shinkaimayano/ttocyobitnA/KiCad Files/ttocyobItnA.kicad_sch

## KiCad design KiCad Files/ttocyobItnA.kicad_sch (2022-06-01)

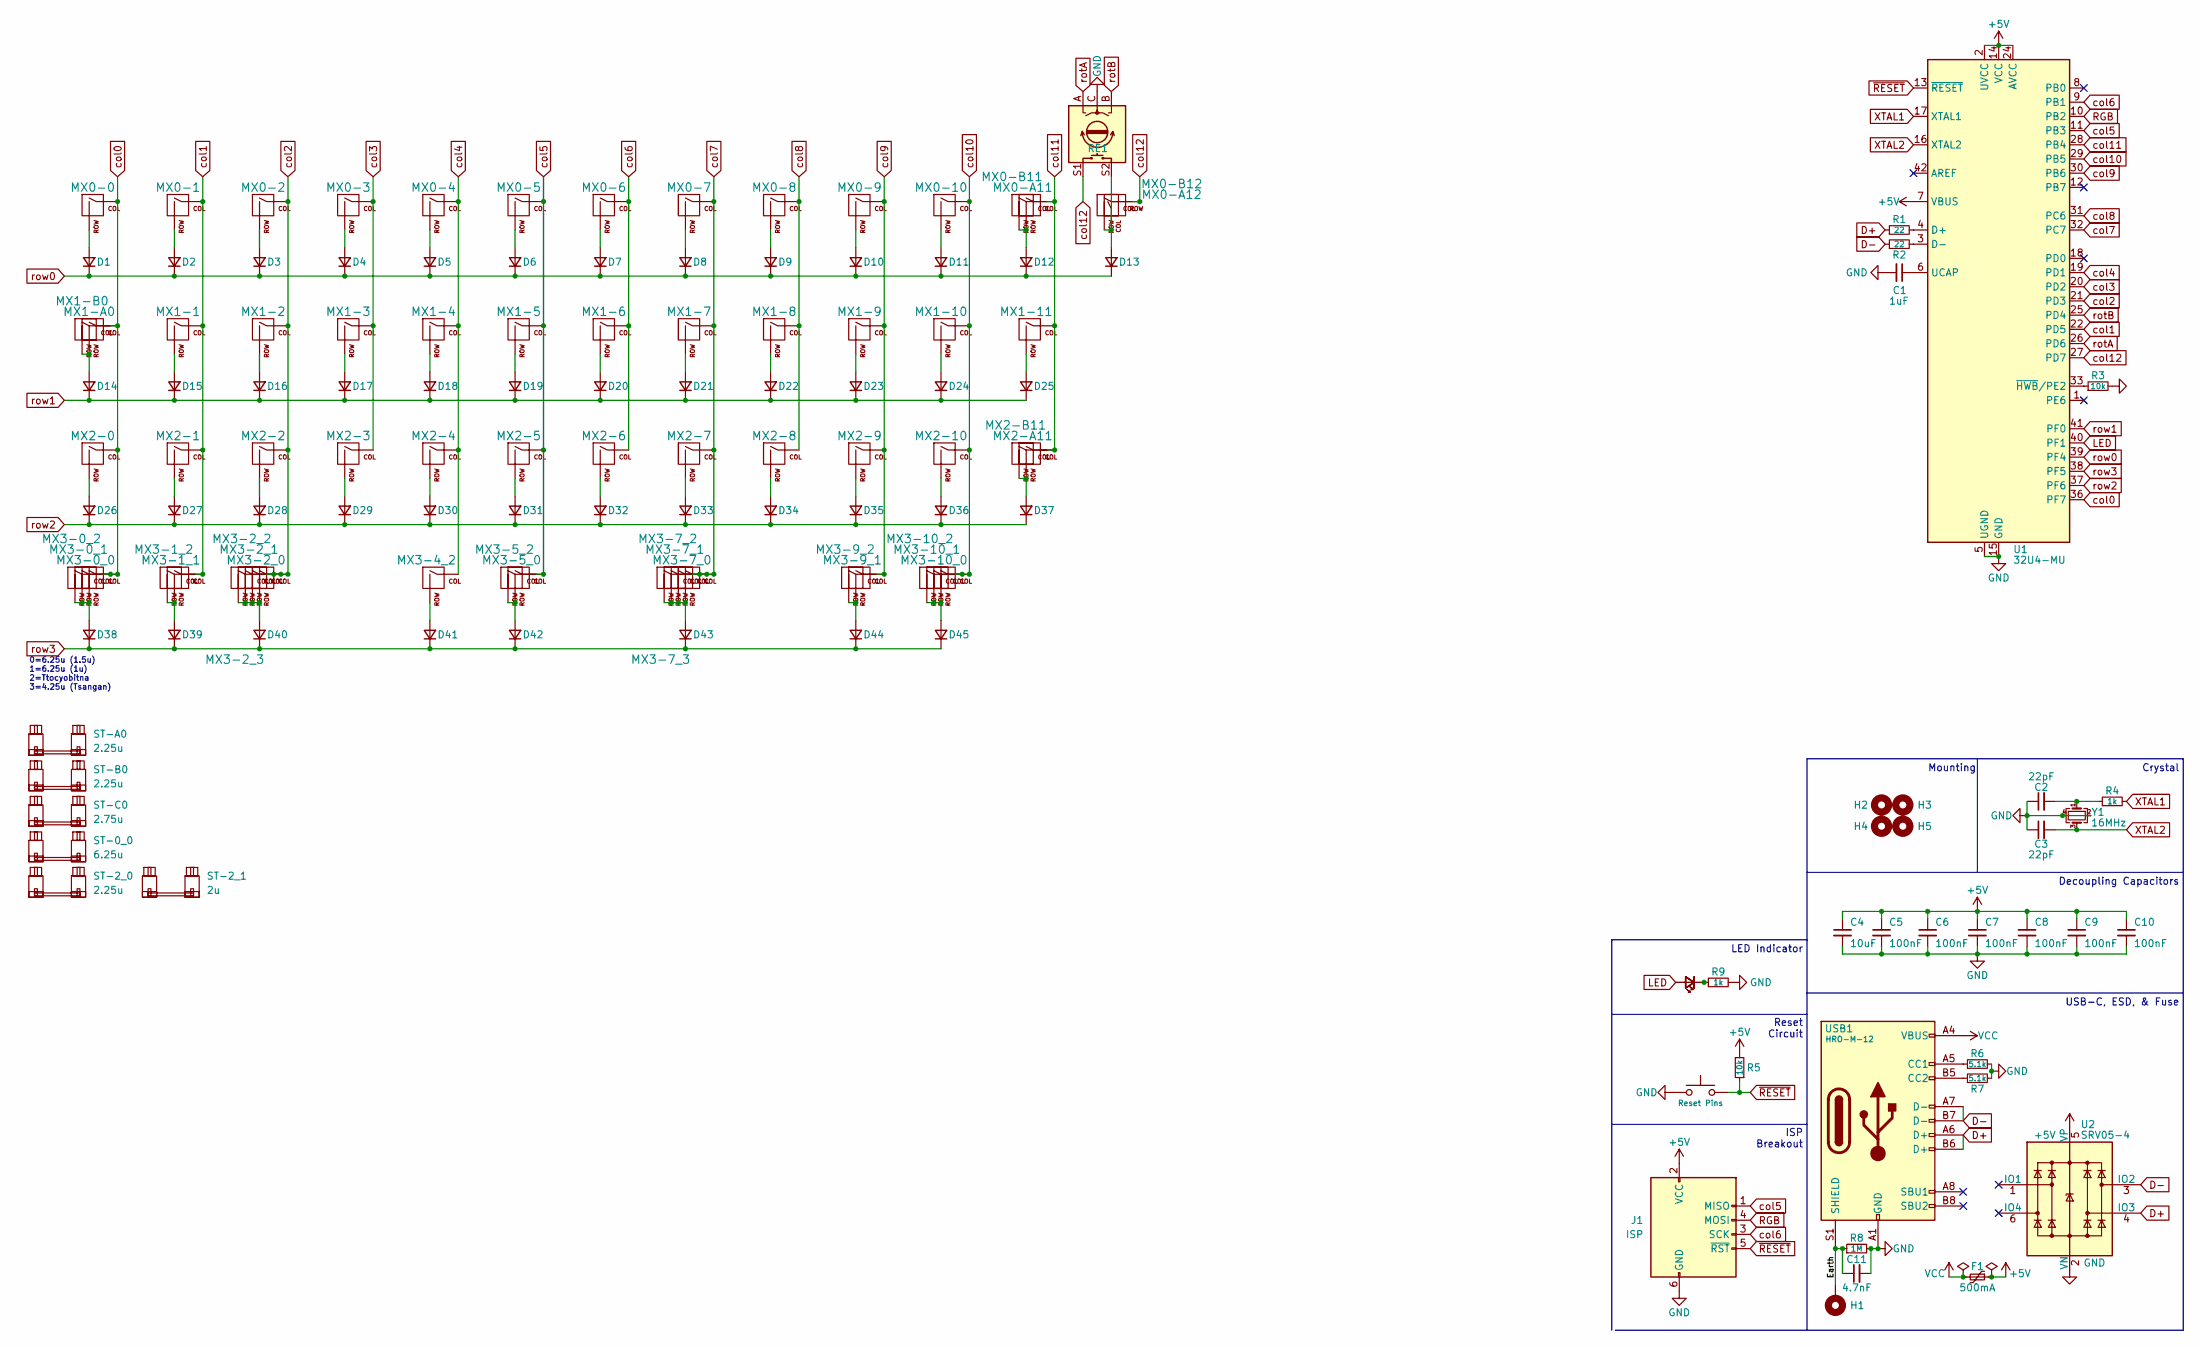
[picture p4: schematic ttocyobItnA.kicad_sch]

Parts:
C1: 1uF; C_0402_1005Metric
C2, C3: 22pF; C_0402_1005Metric
C4: 10uF; C_0402_1005Metric
C5, C6, C7, C8, C9, C10: 100nF; C_0402_1005Metric
C11: 4.7nF; C_0402_1005Metric
D1, D2, D3, D4, D5, D6, D7, D8, D9, D10, D11, D12, D13, D14, D15, D16, D17, D18, D19, D20, D21, D22, D23, D24, D25, D26, D27, D28, D29, D30, D31, D32, D33, D34, D35, D36, D37, D38, D39, D40, D41, D42, D43, D44, D45: D_Small; D_SOD-123
F1: 500mA; Fuse_1206_3216Metric
H1: Earth; MountingHole_2.2mm_M2_Pad_Via
H2, H3, H4, H5: Tray Mount; MountingHole_2.2mm_M2
J1: ISP; PinHeader_2x03_P2.54mm_Vertical
LED1: LED; LED_MX_3mm-FLIPPED
LED2: LED; LED_MX_3mm
MX0-0, MX0-A11, MX0-B12, MX3-0_0, MX3-1_2, MX3-2_0, MX3-2_3, MX3-7_0, MX3-7_3, MX3-9_2, MX3-10_0: MX-NoLED; SW_MX_1.5u
MX0-1, MX0-2, MX0-3, MX0-4, MX0-5, MX0-6, MX0-7, MX0-8, MX0-9, MX0-10, MX0-A12, MX0-B11, MX1-1, MX1-2, MX1-3, MX1-4, MX1-5, MX1-6, MX1-7, MX1-8, MX1-9, MX1-10, MX1-11, MX2-0, MX2-1, MX2-2, MX2-3, MX2-4, MX2-5, MX2-6, MX2-7, MX2-8, MX2-9, MX2-10, MX2-A11, MX3-0_1, MX3-1_1, MX3-2_1, MX3-4_2, MX3-5_0, MX3-5_2, MX3-7_1, MX3-9_1, MX3-10_1: MX-NoLED; SW_MX_1u
MX1-A0, MX2-B11: MX-NoLED; SW_MX_1.75u
MX1-B0: MX-NoLED; SW_MX_1.75u_stp
MX3-0_2, MX3-2_2, MX3-7_2, MX3-10_2: MX-NoLED; SW_MX_1.25u
R1, R2: 22; R_0402_1005Metric
R3, R5: 10k; R_0402_1005Metric
R4, R9: 1k; R_0402_1005Metric
R6, R7: 5.1k; R_0402_1005Metric
R8: 1M; R_0402_1005Metric
RE1: RotaryEncoder_Switch; RotaryEncoder_Alps_EC11E-Switch_Vertical_H20mm
Reset1: Reset Pins; SW_SPST_SKQG_WithStem
ST-0_0: 6.25u; STAB_MX_6.25u
ST-2_0: 2.25u; STAB_MX_2.25u
ST-2_1: 2u; STAB_MX_2u
ST-A0: 2.25u; STAB_MX_2.25u
ST-B0: 2.25u; STAB_MX_2.25u
ST-C0: 2.75u; STAB_MX_2.75u
U1: 32U4-MU; QFN-44-1EP_7x7mm_P0.5mm_EP5.2x5.2mm
U2: SRV05-4; SOT-23-6-routable
USB1: HRO-M-12; USB_C_Receptacle_HRO_TYPE-C-31-M-12
Y1: 16MHz; Crystal_SMD_3225-4Pin_3.2x2.5mm

Connections:
+5V: C4.1, C5.1, C6.1, C7.1, C8.1, C9.1, C10.1, F1.1, J1.2 (VCC), R5.2, U1.2 (UVCC), U1.7 (VBUS), U1.14 (VCC), U1.24 (AVCC), U1.34 (VCC), U1.44 (AVCC), U2.5 (VP)
D+: R1.1, U2.4 (IO3), USB1.A6 (D+), USB1.B6 (D+)
D-: R2.1, U2.3 (IO2), USB1.A7 (D-), USB1.B7 (D-)
Earth: C11.1, H1.1, R8.1, USB1.S1 (SHIELD)
GND: C1.2, C2.1, C3.1, C4.2, C5.2, C6.2, C7.2, C8.2, C9.2, C10.2, C11.2, J1.6 (GND), R3.2, R6.2, R7.2, R8.2, R9.2, RE1.C, Reset1.1, U1.5 (UGND), U1.15 (GND), U1.23 (GND), U1.35 (GND), U1.43 (GND), U1.45 (GND), U2.2 (VN), USB1.A1 (GND), USB1.A12 (GND), USB1.B1 (GND), USB1.B12 (GND), Y1.2, Y1.4
LED: LED1.2 (A), LED2.2 (A), U1.40 (PF1)
unnamed: C1.1, U1.6 (UCAP)
unnamed: C2.2, R4.1, Y1.1
unnamed: D1.2 (A), MX0-0.2 (ROW)
unnamed: D2.2 (A), MX0-1.2 (ROW)
unnamed: D3.2 (A), MX0-2.2 (ROW)
unnamed: D4.2 (A), MX0-3.2 (ROW)
unnamed: D5.2 (A), MX0-4.2 (ROW)
unnamed: D6.2 (A), MX0-5.2 (ROW)
unnamed: D7.2 (A), MX0-6.2 (ROW)
unnamed: D8.2 (A), MX0-7.2 (ROW)
unnamed: D9.2 (A), MX0-8.2 (ROW)
unnamed: D10.2 (A), MX0-9.2 (ROW)
unnamed: D11.2 (A), MX0-10.2 (ROW)
unnamed: D12.2 (A), MX0-A11.2 (ROW), MX0-B11.2 (ROW)
unnamed: D13.2 (A), MX0-A12.1 (COL), MX0-B12.2 (ROW), RE1.S2
unnamed: D14.2 (A), MX1-A0.2 (ROW), MX1-B0.2 (ROW)
unnamed: D15.2 (A), MX1-1.2 (ROW)
unnamed: D16.2 (A), MX1-2.2 (ROW)
unnamed: D17.2 (A), MX1-3.2 (ROW)
unnamed: D18.2 (A), MX1-4.2 (ROW)
unnamed: D19.2 (A), MX1-5.2 (ROW)
unnamed: D20.2 (A), MX1-6.2 (ROW)
unnamed: D21.2 (A), MX1-7.2 (ROW)
unnamed: D22.2 (A), MX1-8.2 (ROW)
unnamed: D23.2 (A), MX1-9.2 (ROW)
unnamed: D24.2 (A), MX1-10.2 (ROW)
unnamed: D25.2 (A), MX1-11.2 (ROW)
unnamed: D26.2 (A), MX2-0.2 (ROW)
unnamed: D27.2 (A), MX2-1.2 (ROW)
unnamed: D28.2 (A), MX2-2.2 (ROW)
unnamed: D29.2 (A), MX2-3.2 (ROW)
unnamed: D30.2 (A), MX2-4.2 (ROW)
unnamed: D31.2 (A), MX2-5.2 (ROW)
unnamed: D32.2 (A), MX2-6.2 (ROW)
unnamed: D33.2 (A), MX2-7.2 (ROW)
unnamed: D34.2 (A), MX2-8.2 (ROW)
unnamed: D35.2 (A), MX2-9.2 (ROW)
unnamed: D36.2 (A), MX2-10.2 (ROW)
unnamed: D37.2 (A), MX2-A11.2 (ROW), MX2-B11.2 (ROW)
unnamed: D38.2 (A), MX3-0_0.2 (ROW), MX3-0_1.2 (ROW), MX3-0_2.2 (ROW)
unnamed: D39.2 (A), MX3-1_1.2 (ROW), MX3-1_2.2 (ROW)
unnamed: D40.2 (A), MX3-2_0.2 (ROW), MX3-2_1.2 (ROW), MX3-2_2.2 (ROW), MX3-2_3.2 (ROW)
unnamed: D41.2 (A), MX3-4_2.2 (ROW)
unnamed: D42.2 (A), MX3-5_0.2 (ROW), MX3-5_2.2 (ROW)
unnamed: D43.2 (A), MX3-7_0.2 (ROW), MX3-7_1.2 (ROW), MX3-7_2.2 (ROW), MX3-7_3.2 (ROW)
unnamed: D44.2 (A), MX3-9_1.2 (ROW), MX3-9_2.2 (ROW)
unnamed: D45.2 (A), MX3-10_0.2 (ROW), MX3-10_1.2 (ROW), MX3-10_2.2 (ROW)
unnamed: LED1.1 (K), LED2.1 (K), R9.1
unnamed: R1.2, U1.4 (D+)
unnamed: R2.2, U1.3 (D-)
unnamed: R3.1, U1.33 (~HWB/PE2)
unnamed: R6.1, USB1.A5 (CC1)
unnamed: R7.1, USB1.B5 (CC2)
RGB: J1.4 (MOSI), U1.10 (PB2)
VCC: F1.2, USB1.A4 (VBUS), USB1.A9 (VBUS), USB1.B4 (VBUS), USB1.B9 (VBUS)
XTAL1: R4.2, U1.17 (XTAL1)
XTAL2: C3.2, U1.16 (XTAL2), Y1.3
col0: MX0-0.1 (COL), MX1-A0.1 (COL), MX1-B0.1 (COL), MX2-0.1 (COL), MX3-0_0.1 (COL), MX3-0_1.1 (COL), MX3-0_2.1 (COL), U1.36 (PF7)
col1: MX0-1.1 (COL), MX1-1.1 (COL), MX2-1.1 (COL), MX3-1_1.1 (COL), MX3-1_2.1 (COL), U1.22 (PD5)
col2: MX0-2.1 (COL), MX1-2.1 (COL), MX2-2.1 (COL), MX3-2_0.1 (COL), MX3-2_1.1 (COL), MX3-2_2.1 (COL), MX3-2_3.1 (COL), U1.21 (PD3)
col3: MX0-3.1 (COL), MX1-3.1 (COL), MX2-3.1 (COL), U1.20 (PD2)
col4: MX0-4.1 (COL), MX1-4.1 (COL), MX2-4.1 (COL), MX3-4_2.1 (COL), U1.19 (PD1)
col5: J1.1 (MISO), MX0-5.1 (COL), MX1-5.1 (COL), MX2-5.1 (COL), MX3-5_0.1 (COL), MX3-5_2.1 (COL), U1.11 (PB3)
col6: J1.3 (SCK), MX0-6.1 (COL), MX1-6.1 (COL), MX2-6.1 (COL), U1.9 (PB1)
col7: MX0-7.1 (COL), MX1-7.1 (COL), MX2-7.1 (COL), MX3-7_0.1 (COL), MX3-7_1.1 (COL), MX3-7_2.1 (COL), MX3-7_3.1 (COL), U1.32 (PC7)
col8: MX0-8.1 (COL), MX1-8.1 (COL), MX2-8.1 (COL), U1.31 (PC6)
col9: MX0-9.1 (COL), MX1-9.1 (COL), MX2-9.1 (COL), MX3-9_1.1 (COL), MX3-9_2.1 (COL), U1.30 (PB6)
col10: MX0-10.1 (COL), MX1-10.1 (COL), MX2-10.1 (COL), MX3-10_0.1 (COL), MX3-10_1.1 (COL), MX3-10_2.1 (COL), U1.29 (PB5)
col11: MX0-A11.1 (COL), MX0-B11.1 (COL), MX1-11.1 (COL), MX2-A11.1 (COL), MX2-B11.1 (COL), U1.28 (PB4)
col12: MX0-A12.2 (ROW), MX0-B12.1 (COL), RE1.S1, U1.27 (PD7)
rotA: RE1.A, U1.26 (PD6)
rotB: RE1.B, U1.25 (PD4)
row0: D1.1 (K), D2.1 (K), D3.1 (K), D4.1 (K), D5.1 (K), D6.1 (K), D7.1 (K), D8.1 (K), D9.1 (K), D10.1 (K), D11.1 (K), D12.1 (K), D13.1 (K), U1.39 (PF4)
row1: D14.1 (K), D15.1 (K), D16.1 (K), D17.1 (K), D18.1 (K), D19.1 (K), D20.1 (K), D21.1 (K), D22.1 (K), D23.1 (K), D24.1 (K), D25.1 (K), U1.41 (PF0)
row2: D26.1 (K), D27.1 (K), D28.1 (K), D29.1 (K), D30.1 (K), D31.1 (K), D32.1 (K), D33.1 (K), D34.1 (K), D35.1 (K), D36.1 (K), D37.1 (K), U1.37 (PF6)
row3: D38.1 (K), D39.1 (K), D40.1 (K), D41.1 (K), D42.1 (K), D43.1 (K), D44.1 (K), D45.1 (K), U1.38 (PF5)
~RESET: J1.5 (~RST), R5.1, Reset1.2, U1.13 (~RESET)

Notes on the sheet:
Mounting
0=6.25u (1.5u) 1=6.25u (1u) 2=Ttocyobitna 3=4.25u (Tsangan)
Crystal
Decoupling Capacitors
LED Indicator
Reset Circuit
USB-C, ESD, & Fuse
ISP Breakout
